Bettys-sidepiece/Yolk-Workshop--Keyboard-Hardware-/Yolk Workshop - Germinal Disc/Simulations/Auto-Power_Switch.asc

M1: pmos; FDS4685
M2: nmos; AP9465GEM
M3: pmos; FDS4685
Q1: pnp; 2N3906
Q2: pnp; 2N3906
R1: res; 10k
R2: res; 10k
R3: res; 25k
R4: res; 1µ
R5: res; 10k
R6: res; 10k
R7: res; 10
V1: voltage; SINE(0 3.7 1)
V2: voltage; 5
V3: voltage; PULSE(0 7 0 1n 1n 0.5 1)
Named nets: 0, VBAT_CTRL, VBUS_CTRL, VSYS_BMS
.tran 2s startup
