Bettys-sidepiece/Yolk-Workshop--Keyboard-Hardware-/Yolk Workshop - Germinal Disc/Simulations/Battery Status LEDs.asc

D1: LED; L1C1-RED1000000000
D2: LED; L1C1-GRN1000000000
M1: nmos; FDW2503NZ
M2: nmos; AONS62814T
R1: res; 1k
R2: res; 1k
R3: res; 1k
V1: voltage; 3.7
V2: voltage; PULSE(0 3.7 0 20n 20n 0.5s 1s)
Named nets: 0
.tran 2s
