Bettys-sidepiece/Yolk-Workshop--Keyboard-Hardware-/Yolk Workshop - Germinal Disc/Simulations/Draft1.asc

M1: nmos; AO6408
M2: pmos; AO6407
R1: res; 10k
R2: res; 25k
R4: res; 100
V1: voltage; 3.3V
V2: voltage; PULSE(0 5 0 1n 1n 0.5s 1s)
V3: voltage; 5V
Named nets: 0
.tran 2s
