Bettys-sidepiece/Yolk-Workshop--Keyboard-Hardware-/Yolk Workshop - Germinal Disc/Simulations/Draft2.asc

M1: pmos; AO6608_P
M2: nmos; BSP89
R1: res; 10
R2: res; 100k
V1: voltage; 5
V2: voltage; PULSE(0 5 0 1n 1n 500m 1s)
Named nets: 0
.tran 3s startup
